psu-epl/EPL-RFID/RFID/demodulation.asc

C1: cap; 1n
C2: cap; 1n
C3: cap; 1n
C4: cap; 1n
C5: cap; 1n
C6: cap; 1n
C7: cap; 2.2n
C8: cap; 1n
C9: cap; 1.1n
D1: diode; 1N4148X
L1: ind; 1.4m
R1: res; 1Meg
R2: res; 1.8k
R3: res; 47k
R4: res; 2.7k
R5: res; 82k
R6: res; 10k
R7: res; 10k
R8: res; 10k
R9: res; 15k
R10: res; 860k
R11: res; 100
R12: res; 10k
R13: res; 20k
R14: res; 10k
U1: UniversalOpamp2
U2: UniversalOpamp2
U3: UniversalOpamp2
U4: UniversalOpamp2
V1: voltage; 12
V2: voltage; 5
V3: voltage; SINE(0 1 15.625k); AC 1
Named nets: 0, 12v, 5v, out
.tran 1m
.model 1N4148X D(Is=2.52n Rs=.568 N=1.752 Cjo=4p M=.4 tt=20n Iave=200m Vpk=15 mfg=OnSemi type=silicon)
